Marspacecraft/PaceandLoveKeyboard/Frameware/PaceAndLoveKeyboard/Core/Oled/oled.c

/*
this library is a 0.91'OLED(ssd1306) driver
*/
#include "string.h"
#include "keyconfig.h"
//Header file reference
//The oledfont.h, oled.h and STM32's i2c.h files need to be referenced in the oled.c file
#include "oled.h"
//#include "oledfont.h"
#include "i2c.h"
#include "timertask.h"

#ifdef I2C_OLED

/*************************8*16ASCII*************************/
static uint8_t F8X16[]=
{
	0x02,0x02,0x02,0x02,0x02,0x02,0x02,0x02,0x80,0x80,0x80,0x80,0x80,0x80,0x80,0x80,// 0
	0x02,0x02,0x02,0xFA,0x02,0x02,0x02,0x02,0x80,0x80,0x80,0xB3,0xB0,0x80,0x80,0x80,//! 1
	0x02,0x22,0x1A,0x0E,0x22,0x1A,0x0E,0x02,0x80,0x80,0x80,0x80,0x80,0x80,0x80,0x80,//" 2
	0x42,0xC2,0x7A,0x42,0xC2,0x7A,0x42,0x02,0x84,0xBF,0x84,0x84,0xBF,0x84,0x84,0x80,//# 3
	0x02,0x72,0x8A,0xFE,0x0A,0x32,0x02,0x02,0x80,0x8C,0x90,0xBF,0x91,0x8E,0x80,0x80,//$ 4
	0xF2,0x0A,0xF2,0x02,0xE2,0x1A,0x02,0x02,0x80,0xA1,0x9C,0x83,0x9E,0xA1,0x9E,0x80,//% 5
	0x02,0xF2,0x0A,0x8A,0x72,0x02,0x02,0x02,0x9E,0xA1,0xA3,0xA4,0x99,0xA7,0xA1,0x90,//& 6
	0x22,0x2E,0x1E,0x02,0x02,0x02,0x02,0x02,0x80,0x80,0x80,0x80,0x80,0x80,0x80,0x80,//' 7
	0x02,0x02,0x02,0xE2,0x1A,0x06,0x02,0x02,0x80,0x80,0x80,0x87,0x98,0xA0,0x80,0x80,//( 8
	0x02,0x02,0x06,0x1A,0xE2,0x02,0x02,0x02,0x80,0x80,0xA0,0x98,0x87,0x80,0x00,0x00,//) 9
	0x22,0x42,0x82,0xF2,0x82,0x42,0x22,0x02,0x84,0x82,0x81,0x8F,0x81,0x82,0x84,0x80,//* 10
	0x02,0x02,0x02,0xF2,0x02,0x02,0x02,0x02,0x81,0x81,0x81,0x9F,0x81,0x81,0x81,0x80,//+ 11
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
	0x02,0x02,0x32,0x72,0x72,0x72,0xF2,0xFE,
	0xCF,0x8E,0x9E,0x9E,0x8C,0x80,0xC0,0xFF,//5
	0x06,0x02,0x72,0x72,0x72,0x62,0xE6,0xFE,
	0xC0,0x80,0x9E,0x9E,0x9E,0x80,0xC0,0xFF,//6
	0xF2,0xF2,0x72,0x12,0x02,0x82,0xE2,0xFE,
	0xFF,0xFF,0x80,0x80,0xFF,0xFF,0xFF,0xFF,//7



};
/**
 * 0.91 "OLED initialization control word
 * Each control word can change the display properties of the screen according to the manufacturer's Datasheet
 * For example, in the fifth line from the bottom, the control word 0x81,0x80.you can changes the contrast by changing 0x80
 * 
*/
#if 0
uint8_t initcmd1[] = 
{
	0xAE,		//display off
	0xD5, 0x80, //Set Display Clock Divide Ratio/Oscillator Frequency
	0xA8, 0x1F, //set multiplex Ratio
	0xD3, 0x00, //display offset
	0x40,		//set display start line
	0x8d, 0x14, //set charge pump
	0xa0,		//set segment remap
	0xc0,		//set com output scan direction
	0xda, 0x00, //set com pins hardware configuration
	0x81, 0x80, //set contrast control
	0xd9, 0x1f, //set pre-charge period
	0xdb, 0x40, //set vcom deselect level
	0xa4,		//Set Entire Display On/Off
	0xaf,		//set display on
};
	#endif
	uint8_t initcmd1[] = {
	0xAE,		//display off
	0xD5, 0x80, //Set Display Clock Divide Ratio/Oscillator Frequency
	0xA8, 0x1F, //set multiplex Ratio
	0xD3, 0x00, //display offset
	0x40,		//set display start line
	0x8d, 0x14, //set charge pump
	//0x27,
	//0x2e,
	0xa0,		//set segment remap
	0xc0,		//set com output scan direction
	0xda, 0x00, //set com pins hardware configuration
	0x81, 0x80, //set contrast control
	0xd9, 0x1f, //set pre-charge period
	0xdb, 0x40, //set vcom deselect level
	0xa4,		//Set Entire Display On/Off
	0xaf,		//set display on
};
/**
 * OLED writes commands and data functions
 * OLED writes commands, data functions, and changes the contents of these two functions if you want to migrate them to another development board
 * For example: I use the i2c2 interface, then you only need to change &hi2c1 to &hi2c2.
**/
void OLED_Write_cmd(uint8_t cmd)
{
	HAL_I2C_Mem_Write(&hi2c2, 0x78, 0x00, I2C_MEMADD_SIZE_8BIT, &cmd, 1, 0x100);
}
void OLED_Write_data(uint8_t data)
{
	HAL_I2C_Mem_Write(&hi2c2, 0x78, 0x40, I2C_MEMADD_SIZE_8BIT, &data, 1, 0x100);
}

void OLED_Write_databuffer(uint8_t* data,uint16_t len)
{
	HAL_I2C_Mem_Write(&hi2c2, 0x78, 0x40, I2C_MEMADD_SIZE_8BIT, data, len, 0x100);
}


/**
 * @brief	Image display function
 * @param x0  Image display start position x-axis
 * @param y0  Image display start position y-axis
 * @param x1  Image display end position x-axis 1 - 127
 * @param y1  Image display end position x-axis 1 - 4
 * @param BMP Image display pointer address
 * @note	The image needs to be converted to an array and passed into this function
*/
void OLED_ShowPic(uint8_t x0, uint8_t y0, uint8_t x1, uint8_t y1, uint8_t BMP[])
{
	uint16_t i = 0;
	uint8_t y;
	for (y = y0; y < y1; y++)
	{
		OLED_Set_Position(x0, y);
		OLED_Write_databuffer(&BMP[i],x1-x0);
		i+=x1-x0;
	}
}



/**
 * @brief	Display a float 
 * @param x  position x-axis  0 - 127
 * @param y  position y-axis  0
 * @param num  The order of the Chinese characters in the Hzb[] array
 * @param accuracy Preserve decimal places
 * @param fontsize 8/16
 * @note	
*/
void OLED_ShowFloat(uint8_t x, uint8_t y, float num, uint8_t accuracy)
{
	uint8_t i = 0;
	uint8_t j = 0;
	uint8_t t = 0;
	uint8_t temp = 0;
	uint16_t numel = 0;
	uint32_t integer = 0;
	float decimals = 0;

	//Is a negative number?
	if (num < 0)
	{
		OLED_ShowChar(x, y, '-');
		num = 0 - num;
		i++;
	}

	integer = (uint32_t)num;
	decimals = num - integer;

	//Integer part
	if (integer)
	{
		numel = integer;

		while (numel)
		{
			numel /= 10;
			j++;
		}
		i += (j - 1);
		for (temp = 0; temp < j; temp++)
		{
			OLED_ShowChar(x + 14 * (i - temp), y, integer % 10 + '0'); // 鏄剧ず鏁存暟閮ㄥ垎
			integer /= 10;
		}
	}
	else
	{
		OLED_ShowChar(x + 14 * i, y, temp + '0');
	}
	i++;
	//Decimal part
	if (accuracy)
	{
		OLED_ShowChar(x + 14 * i, y, '.');

		i++;
		for (t = 0; t < accuracy; t++)
		{
			decimals *= 10;
			temp = (uint8_t)decimals;
			OLED_ShowChar(x + 14 * (i + t), y, temp + '0');
			decimals -= temp;
		}
	}
}

/**
 * @brief	OLED pow function
 * @param m - base
 * @param n - exponent
 * @return result
*/
static uint32_t OLED_Pow(uint8_t a, uint8_t n)
{
	uint32_t result = 1;
	while (n--)
	{
		result *= a;
	}
	return result;
}

/**
 * @brief	Display a uint32 Interger
 * @param x  position x-axis  0 - 127
 * @param y  position y-axis  0 - 3
 * @param num  Displayed integers
 * @param length Number of integer digits
 * @note	
*/
void OLED_ShowNum(uint8_t x, uint8_t y, uint32_t num, uint8_t length)
{

	uint8_t t, temp;
	uint8_t enshow = 0;
	for (t = 0; t < length; t++)
	{
		temp = (num / OLED_Pow(10, length - t - 1)) % 10;
		if (enshow == 0 && t < (length - 1))
		{
			if (temp == 0)
			{
				OLED_ShowChar(x + 14 * t, y, ' ');
				continue;
			}
			else
				enshow = 1;
		}
		OLED_ShowChar(x + 14 * t, y, temp + '0');
	}
}


/**
 * @brief	Display ascii string
 * @param x  String start position on the X-axis  range锛? - 127
 * @param y  String start position on the Y-axis  range锛? - 3 
 * @param ch  String pointer
 * @param fontsize You can choose from two fonts 8/16
**/
void OLED_ShowStr(uint8_t x, uint8_t y, char *ch)
{
	uint8_t j = 0;
	while (ch[j] != '\0')
	{
		OLED_ShowChar(x, y, ch[j]);
		x += 8;
		j++;
	}
}

/**
 * @brief	Displays ASCII characters
 * @param x  Character position on the X-axis  range锛? - 127
 * @param y  Character position on the Y-axis  range锛? - 3 
 * @param no  character
 * @param fontsize You can choose from three fonts 8/16
**/
void OLED_ShowChar(uint8_t x, uint8_t y, uint8_t ch)
{
	uint8_t c = 0;
	c = ch - ' ';

	if (x > 127 || y>4) //beyond the right boundary
	{
		return;
	}

	OLED_Set_Position(x, y);
	OLED_Write_databuffer(&F8X16[c * 16],8);

	if(y<3)
	{
		OLED_Set_Position(x, y+1);
		OLED_Write_databuffer(&F8X16[c * 16+8],8);
	}
}


/**
 * OLED fill function, after using the function 0.91 inch oled screen into full white
**/
void OLED_Allfill(void)
{
	uint8_t i, j;
	for (i = 0; i < 4; i++)
	{
		OLED_Write_cmd(0xb0 + i);
		OLED_Write_cmd(0x00);
		OLED_Write_cmd(0x10);
		for (j = 0; j < 128; j++)
		{
			OLED_Write_data(0xFF);
		}
	}
}

/**
 * @brief Set coordinates
 * @param x: X position, range 0 - 127  Because our OLED screen resolution is 128*32, so the horizontal is 128 pixels
 * @param y: Y position, range 0 - 3    Because the vertical pixels are positioned in pages, each page has 8 pixels, so there are 4 pages
**/
void OLED_Set_Position(uint8_t x, uint8_t y)
{
	OLED_Write_cmd(0xb0 + y);
	OLED_Write_cmd(((x & 0xf0) >> 4) | 0x10);
	OLED_Write_cmd((x & 0x0f) | 0x00);
}
/**
 * Clear Screen Function
 * Fill each row and column with 0
**/
void OLED_Clear(void)
{
	uint8_t i, n;
	for (i = 0; i < 4; i++)
	{
		OLED_Write_cmd(0xb0 + i);
		OLED_Write_cmd(0x00);
		OLED_Write_cmd(0x10);
		for (n = 0; n < 128; n++)
		{
			OLED_Write_data(0);
		}
	}
}
/**
 * Turn screen display on and off
**/
void OLED_Display_On(void)
{
	OLED_Write_cmd(0x8D);
	OLED_Write_cmd(0x14);
	OLED_Write_cmd(0xAF);
}
void OLED_Display_Off(void)
{
	OLED_Write_cmd(0x8D);
	OLED_Write_cmd(0x10);
	OLED_Write_cmd(0xAF);
}

/**
 * Initialize the screen
 * Function:send control words one by one
**/
void OLED_Init(void)
{

	HAL_Delay(100);
	uint8_t i;
	for (i = 0; i < sizeof(initcmd1); i++)
	{

		OLED_Write_cmd(initcmd1[i]); //display off
	}

	OLED_Clear();
	OLED_Set_Position(0, 0);
}

///*************************************///


typedef struct
{
	uint8_t 	title_enable;
	uint8_t 	title_flowfg;//列字符溢出标志	
	
	uint16_t 	title_buflen;
	uint16_t 	title_showpos;//列显示开始位置
	uint8_t 	title_showposdelay;//列滚动开始延时
	
	
}oledtile;


typedef struct
{
	oledtile titles[OLED_BUFFER_HEIGHT];
	
	uint8_t line_showorder[OLED_BUFFER_HEIGHT];//滚动显示列顺序队列
	uint8_t linepos;//当前起始显示队列
	uint8_t linenum;//显示列个数
	
}oledbufmsg_t;

static oledbufmsg_t sg_oledbuffermsg = {0};
static uint8_t sg_oledbuffer[2*OLED_BUFFER_HEIGHT][OLED_BUFFER_WIDTH] ={0};


static void Oled_Title2ShowOrder(uint8_t title)
{
	uint8_t i=0;
	for(i=0;i<sg_oledbuffermsg.linenum;i++)
	{
		if(sg_oledbuffermsg.line_showorder[i] == title)
			return;

	}

	if(i<OLED_BUFFER_HEIGHT)
	{
		sg_oledbuffermsg.line_showorder[i] = title;
		sg_oledbuffermsg.linenum++;
	}
}

void OLED_CharMode_SetShowOrder(uint8_t* titles)
{
	uint8_t i;
	for(i=0;i<OLED_BUFFER_HEIGHT;i++)
	{
		if(OLED_TITLE_NULL <= titles[i])
		{	
			break;
		}
		sg_oledbuffermsg.line_showorder[i] = titles[i];
	}

	sg_oledbuffermsg.linenum = i;
	sg_oledbuffermsg.linepos = 0;
}

void OLED_CharMode_ClearShowOrder()
{
	sg_oledbuffermsg.linenum = 0;
	sg_oledbuffermsg.linepos = 0;

}


static void Oled_ShowTitle2Line(uint8_t title,uint8_t line)
{
	uint16_t i = 0;
	uint16_t title_buflen;
	uint16_t title_showpos;//列显示开始位置
	uint8_t j;

	if(title>=OLED_BUFFER_HEIGHT || line>=2)
		return;

	line = line << 1;
	if(0 == sg_oledbuffermsg.titles[title].title_enable)
		return;

	title_buflen = sg_oledbuffermsg.titles[title].title_buflen;
	title_showpos = sg_oledbuffermsg.titles[title].title_showpos;
	title = title << 1;
	for(j=0;j<2;j++,line++)
	{
		OLED_Set_Position(0, line);
		
		OLED_Write_databuffer(&sg_oledbuffer[title+j][0], 8);
		
		i = title_buflen - title_showpos;
		if(i>120)
		{
			i = 120;
		}
		OLED_Write_databuffer(&sg_oledbuffer[title+j][title_showpos], i);
		
		i+=8;
		for (; i <OLED_WIDTH; i++)
		{
			OLED_Write_data(0x00);
		}
	}
}


static uint8_t Oled_Append2Title(uint8_t title,uint8_t* font,uint16_t len)
{
	oledtile* titlemsg;
	uint8_t ret = true;
	if(title>=OLED_BUFFER_HEIGHT)
		return false;

	titlemsg = &sg_oledbuffermsg.titles[title];

	if((len + titlemsg->title_buflen)>OLED_BUFFER_WIDTH)
	{
		len = OLED_BUFFER_WIDTH - titlemsg->title_buflen;
		ret = false;
	}

	if(titlemsg->title_buflen>OLED_WIDTH)
	{
		titlemsg->title_flowfg = 1;
	}

	title = title << 1;
	memcpy(sg_oledbuffer[title]+titlemsg->title_buflen,font,len);
	memcpy(sg_oledbuffer[title+1]+titlemsg->title_buflen,font+len,len);
	titlemsg->title_buflen += len;
	return ret;
	
}

static void Oled_Reset2Title(uint8_t title,uint8_t* font,uint16_t len)
{
	oledtile* titlemsg;
	if(title>=OLED_BUFFER_HEIGHT)
		return;
	
	titlemsg = &sg_oledbuffermsg.titles[title];
	if(NULL == font)
	{
		titlemsg->title_enable = 0;
		return;
	}
	titlemsg->title_enable = 1;
	titlemsg->title_buflen = 8;
	titlemsg->title_showpos = 8;
	titlemsg->title_showposdelay = 15;
	

	
	memcpy(sg_oledbuffer[2*title],&TITLEF[16*title],8);
	memcpy(sg_oledbuffer[2*title+1],&TITLEF[16*title+8],8);

	Oled_Append2Title(title,font,len);

}

static void Oled_Flush_Line(uint8_t lineflushfg)
{
	uint8_t line,title,i,num;
	oledtile* titlemsg;
	num = (2<sg_oledbuffermsg.linenum)?2:sg_oledbuffermsg.linenum;

	line=sg_oledbuffermsg.linepos;
	
	for(i=0;i<num;)
	{	
		title = sg_oledbuffermsg.line_showorder[line];
		titlemsg = &sg_oledbuffermsg.titles[title];
		if(titlemsg->title_enable)
		{
			if(lineflushfg)//刷新所有行
			{
				Oled_ShowTitle2Line(title,i);
			}
			else
			{//只刷新溢出行
				if(titlemsg->title_flowfg)
				{
					if(0==titlemsg->title_showposdelay)
					{
						titlemsg->title_showpos += 2;
						if((titlemsg->title_buflen - titlemsg->title_showpos)<=80)
						{
							titlemsg->title_showpos = 8;
							titlemsg->title_showposdelay = 15;
						}
						Oled_ShowTitle2Line(title,i);
					}
					else
					{
						titlemsg->title_showposdelay--;
					}
				}
			}
			i++;
		}
		
		line++;
		line %= sg_oledbuffermsg.linenum;
		if(line == sg_oledbuffermsg.linepos)
		{
			break;
		}
	}
}

void OLED_CharMode_ShowString(uint8_t title,uint8_t* string)
{
	uint16_t i,len;
	if(title>=OLED_BUFFER_HEIGHT || string[0] < ' ')
		return;

	Oled_Reset2Title(title,&F8X16[(string[0]-' ')*16],8);
	len = strlen((char*)string);
	for(i=1;i<len;i++)
	{
		if(false == Oled_Append2Title(title,&F8X16[(string[i]-' ')*16],8))
		{
			break;
		}
	}
	Oled_Title2ShowOrder(title);
	Oled_Flush_Line(true);
}

void OLED_CharMode_ShowStringAppend(uint8_t title,uint8_t* string)
{
	uint16_t i,len;
	if(title>=OLED_BUFFER_HEIGHT)
		return;
	len = strlen((char*)string);
	for(i=0;i<len;i++)
	{
		if(false == Oled_Append2Title(title,&F8X16[(string[i]-' ')*16],8))
		{
			break;
		}
	}
	
	Oled_Flush_Line(true);
}



void OLED_CharMode_Flush(uint8_t* arg)
{
	static uint8_t linetime = 30;

	if((sg_oledbuffermsg.linenum > 2)&&(0 == linetime))
	{
		sg_oledbuffermsg.linepos += 2;
		if(sg_oledbuffermsg.linepos >= sg_oledbuffermsg.linenum)
			sg_oledbuffermsg.linepos = 0;
		linetime = 30;
		Oled_Flush_Line(true);
		return;
	}
	linetime--;

	Oled_Flush_Line(false);

}




static CycleTimerHandler* sg_oledtimer = NULL;

void OLED_CharMode_DeInit()
{
	if(sg_oledtimer)
	{
		Stop_CycleTimer(sg_oledtimer);
		sg_oledtimer = NULL;
	}
	OLED_Display_Off();
}

void OLED_CharMode_Init()
{
	memset(sg_oledbuffer,0,sizeof(sg_oledbuffer));
	memset(&sg_oledbuffermsg,0,sizeof(sg_oledbuffermsg));
	OLED_Clear();
	OLED_Set_Position(0, 0);
	
	if(NULL == sg_oledtimer)
	{
		sg_oledtimer = Start_CycleTimer(TIMER_PERIOD_100MS,OLED_CharMode_Flush,NULL);
	}
	OLED_Display_On();
}

uint8_t ikun[512] = { /* 0XE3,0X01,0X20,0X00,0X80,0X00, */
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

};




void ginisobeautiful()
{
	
	OLED_Init();
	/*
	uint8_t i,j;

	for(j=0;j<90;j++)
	{
		for(i=0;i<SHARINGAN_NUM;i++)
		{
			OLED_ShowPic(0,0,32,4,Sharingan[i]);
			HAL_Delay(10);
		}
	}
	*/
	OLED_ShowPic(0,0,128,4,ikun);

	
}


#ifdef TEST_OLED
#include "tracelog.h"

unsigned char BMP1[] =
{
 
0x00,0x00,0x00,0x00,0x00,0xE0,0xF8,0x7C,0x0E,0x06,0x87,0x87,0x87,0x87,0x87,0x87,
0x87,0x87,0x87,0x87,0x87,0x87,0x87,0x87,0x87,0x87,0x87,0x0E,0x1E,0xFC,0xF8,0xE0,
0x80,0xE0,0xF0,0x38,0x38,0xFF,0xFF,0x00,0x00,0x00,0xC1,0xE1,0xC1,0x01,0x01,0x01,
0xC1,0xC1,0xC1,0xC1,0xC1,0xC1,0xC1,0xC1,0xC1,0xC1,0xC1,0x00,0x00,0xFF,0xFF,0xFF,
0xFF,0xFF,0xFF,0x00,0x00,0xFF,0xFF,0x00,0x00,0x00,0x18,0x18,0x18,0x18,0x18,0x18,
0x18,0x00,0x00,0x00,0x18,0x18,0x18,0x18,0x18,0x18,0x18,0x00,0x00,0xFF,0xFF,0xFF,
0x07,0x1F,0x3F,0x78,0x70,0xE3,0xE3,0xE0,0xC0,0xC0,0xC3,0xC3,0xC3,0xC3,0xC3,0xC3,
0xC3,0xC0,0xC0,0xC0,0xC3,0xC3,0xC3,0xC3,0xE0,0xE0,0xE0,0x70,0x78,0x3F,0x1F,0x07,/*"C:\Users\kkk\Desktop\news.bmp",0*/ 
};


void test_oled()
{
	float numberfu=-12.1;

	OLED_Allfill();
    HAL_Delay(500);

	OLED_Clear();
    //OLED_ShowPic(90,0,122,4,BMP1);
	//HAL_Delay(5000);
	//OLED_ShowStr(0,3,"Hello");
	//OLED_ShowFloat(50,0,numberfu,3);
	OLED_ShowStr(0,0,"Hello World");
	//OLED_ShowStr(0,1,"I.m");
	OLED_ShowStr(0,2,"I'm Marspacecraft!");
	HAL_Delay(5000);
	//OLED_Clear();
}

void test_charmode()
{
	OLED_CharMode_Init();
	OLED_CharMode_ShowString(OLED_TITLE_0,"Hello0 abcdefghijklmnopqrstuw");
	OLED_CharMode_ShowString(OLED_TITLE_1,"Hello1");
	OLED_CharMode_ShowString(OLED_TITLE_3,"Hello3");
	OLED_CharMode_ShowString(OLED_TITLE_4,"Hello4");
	OLED_CharMode_ShowString(OLED_TITLE_7,"Hello7");
	OLED_CharMode_ShowString(OLED_TITLE_6,"Hello6");
	HAL_Delay(3000);
}

void test_charmodeflush()
{
	OLED_CharMode_Init();
	
	OLED_CharMode_ShowString(OLED_TITLE_0,"Hello0");
	OLED_CharMode_ShowString(OLED_TITLE_1,"Hello1 abcdefghijklmnopqrstuw");
	OLED_CharMode_ShowString(OLED_TITLE_2,"Hello2");
	OLED_CharMode_ShowString(OLED_TITLE_3,"Hello3 abcdefghijklmnopqrstuw");
	OLED_CharMode_ShowString(OLED_TITLE_4,"Hello4 abcdefghijklmnopqrstuw");
	OLED_CharMode_ShowString(OLED_TITLE_5,"Hello5 abcdefghijklmnopqrstuw");
	
	while(1)
	{
		OLED_CharMode_Flush(NULL);
		HAL_Delay(100);
	}
}
void testcase_oled()
{
	TRACELOG_DEBUG("Running testcase_oled");
	//test_oled();
	test_charmode();
	//test_charmodeflush();
	TRACELOG_DEBUG("Testcase_oled end");
}

#endif

#endif
