Marspacecraft/PaceandLoveKeyboard/Frameware/PaceAndLoveKeyboard/Core/Src/spi.c

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
/* Includes ------------------------------------------------------------------*/
#include "spi.h"

/* USER CODE BEGIN 0 */
volatile static EXT_CSFUNC sg_EXT_SPI_CsFunc = NULL;

/* USER CODE END 0 */

SPI_HandleTypeDef hspi1;
SPI_HandleTypeDef hspi2;
SPI_HandleTypeDef hspi3;
DMA_HandleTypeDef hdma_spi2_tx;
DMA_HandleTypeDef hdma_spi3_rx;
DMA_HandleTypeDef hdma_spi3_tx;

/* SPI1 init function */
void MX_SPI1_Init(void)
{

  /* USER CODE BEGIN SPI1_Init 0 */
  GPIO_InitTypeDef GPIO_InitStruct = {0};

  /* USER CODE END SPI1_Init 0 */

  hspi1.Instance = SPI1;
  hspi1.Init.Mode = SPI_MODE_MASTER;
  hspi1.Init.Direction = SPI_DIRECTION_2LINES_RXONLY;
  hspi1.Init.DataSize = SPI_DATASIZE_8BIT;
  hspi1.Init.CLKPolarity = SPI_POLARITY_HIGH;
  hspi1.Init.CLKPhase = SPI_PHASE_1EDGE;
  hspi1.Init.NSS = SPI_NSS_SOFT;
  hspi1.Init.BaudRatePrescaler = SPI_BAUDRATEPRESCALER_16;
  hspi1.Init.FirstBit = SPI_FIRSTBIT_MSB;
  hspi1.Init.TIMode = SPI_TIMODE_DISABLE;
  hspi1.Init.CRCCalculation = SPI_CRCCALCULATION_DISABLE;
  hspi1.Init.CRCPolynomial = 10;
  if (HAL_SPI_Init(&hspi1) != HAL_OK)
  {
    Error_Handler();
  }
  /* USER CODE BEGIN SPI1_Init 2 */
	__HAL_RCC_GPIOA_CLK_ENABLE(); 	  
	GPIO_InitStruct.Pin =  KEY_PL_Pin;  
	GPIO_InitStruct.Mode	= GPIO_MODE_OUTPUT_PP;	
	GPIO_InitStruct.Pull	= GPIO_PULLUP;
	GPIO_InitStruct.Speed = GPIO_SPEED_FREQ_HIGH;
	HAL_GPIO_Init(KEY_PL_GPIO_Port, &GPIO_InitStruct);  
	  
	  
	HAL_GPIO_WritePin(KEY_PL_GPIO_Port,KEY_PL_Pin,GPIO_PIN_RESET);

  /* USER CODE END SPI1_Init 2 */

}
/* SPI2 init function */
void MX_SPI2_Init(void)
{

  hspi2.Instance = SPI2;
  hspi2.Init.Mode = SPI_MODE_MASTER;
  hspi2.Init.Direction = SPI_DIRECTION_2LINES;
  hspi2.Init.DataSize = SPI_DATASIZE_8BIT;
  hspi2.Init.CLKPolarity = SPI_POLARITY_LOW;
  hspi2.Init.CLKPhase = SPI_PHASE_1EDGE;
  hspi2.Init.NSS = SPI_NSS_SOFT;
  hspi2.Init.BaudRatePrescaler = SPI_BAUDRATEPRESCALER_64;
  hspi2.Init.FirstBit = SPI_FIRSTBIT_MSB;
  hspi2.Init.TIMode = SPI_TIMODE_DISABLE;
  hspi2.Init.CRCCalculation = SPI_CRCCALCULATION_DISABLE;
  hspi2.Init.CRCPolynomial = 10;
  if (HAL_SPI_Init(&hspi2) != HAL_OK)
  {
    Error_Handler();
  }
}
/* SPI3 init function */
void MX_SPI3_Init(void)
{

  hspi3.Instance = SPI3;
  hspi3.Init.Mode = SPI_MODE_MASTER;
  hspi3.Init.Direction = SPI_DIRECTION_2LINES;
  hspi3.Init.DataSize = SPI_DATASIZE_8BIT;
  hspi3.Init.CLKPolarity = SPI_POLARITY_LOW;
  hspi3.Init.CLKPhase = SPI_PHASE_1EDGE;
  hspi3.Init.NSS = SPI_NSS_SOFT;
  hspi3.Init.BaudRatePrescaler = SPI_BAUDRATEPRESCALER_16;
  hspi3.Init.FirstBit = SPI_FIRSTBIT_MSB;
  hspi3.Init.TIMode = SPI_TIMODE_DISABLE;
  hspi3.Init.CRCCalculation = SPI_CRCCALCULATION_DISABLE;
  hspi3.Init.CRCPolynomial = 10;
  if (HAL_SPI_Init(&hspi3) != HAL_OK)
  {
    Error_Handler();
  }
}

void HAL_SPI_MspInit(SPI_HandleTypeDef* spiHandle)
{

  GPIO_InitTypeDef GPIO_InitStruct = {0};
  if(spiHandle->Instance==SPI1)
  {
    /* SPI1 clock enable */
    __HAL_RCC_SPI1_CLK_ENABLE();

    __HAL_RCC_GPIOA_CLK_ENABLE();
    /**SPI1 GPIO Configuration
    PA5     ------> SPI1_SCK
    PA6     ------> SPI1_MISO
    */
    GPIO_InitStruct.Pin = KEY_SPI1_SCK_Pin;
    GPIO_InitStruct.Mode = GPIO_MODE_AF_PP;
    GPIO_InitStruct.Speed = GPIO_SPEED_FREQ_HIGH;
    HAL_GPIO_Init(KEY_SPI1_SCK_GPIO_Port, &GPIO_InitStruct);

    GPIO_InitStruct.Pin = KEY_SPI1_MISO_Pin;
    GPIO_InitStruct.Mode = GPIO_MODE_INPUT;
    GPIO_InitStruct.Pull = GPIO_NOPULL;
    HAL_GPIO_Init(KEY_SPI1_MISO_GPIO_Port, &GPIO_InitStruct);

  }
  else if(spiHandle->Instance==SPI2)
  {
    /* SPI2 clock enable */
    __HAL_RCC_SPI2_CLK_ENABLE();

    __HAL_RCC_GPIOB_CLK_ENABLE();
    /**SPI2 GPIO Configuration
    PB13     ------> SPI2_SCK
    PB14     ------> SPI2_MISO
    PB15     ------> SPI2_MOSI
    */
    GPIO_InitStruct.Pin = EXT_SPI2_CLK_Pin|EXT_SPI2_MOSI_Pin;
    GPIO_InitStruct.Mode = GPIO_MODE_AF_PP;
    GPIO_InitStruct.Speed = GPIO_SPEED_FREQ_HIGH;
    HAL_GPIO_Init(GPIOB, &GPIO_InitStruct);

    GPIO_InitStruct.Pin = EXT_SPI2_MISO_Pin;
    GPIO_InitStruct.Mode = GPIO_MODE_INPUT;
    GPIO_InitStruct.Pull = GPIO_NOPULL;
    HAL_GPIO_Init(EXT_SPI2_MISO_GPIO_Port, &GPIO_InitStruct);

    /* SPI2 DMA Init */
    /* SPI2_TX Init */
    hdma_spi2_tx.Instance = DMA1_Channel5;
    hdma_spi2_tx.Init.Direction = DMA_MEMORY_TO_PERIPH;
    hdma_spi2_tx.Init.PeriphInc = DMA_PINC_DISABLE;
    hdma_spi2_tx.Init.MemInc = DMA_MINC_ENABLE;
    hdma_spi2_tx.Init.PeriphDataAlignment = DMA_PDATAALIGN_BYTE;
    hdma_spi2_tx.Init.MemDataAlignment = DMA_MDATAALIGN_BYTE;
    hdma_spi2_tx.Init.Mode = DMA_NORMAL;
    hdma_spi2_tx.Init.Priority = DMA_PRIORITY_LOW;
    if (HAL_DMA_Init(&hdma_spi2_tx) != HAL_OK)
    {
      Error_Handler();
    }

    __HAL_LINKDMA(spiHandle,hdmatx,hdma_spi2_tx);

  }
  else if(spiHandle->Instance==SPI3)
  {
    /* SPI3 clock enable */
    __HAL_RCC_SPI3_CLK_ENABLE();

    __HAL_RCC_GPIOB_CLK_ENABLE();
    /**SPI3 GPIO Configuration
    PB3     ------> SPI3_SCK
    PB4     ------> SPI3_MISO
    PB5     ------> SPI3_MOSI
    */
    GPIO_InitStruct.Pin = FLASH_SPI3_CLK_Pin|FLASH_SPI3_MOSI_Pin;
    GPIO_InitStruct.Mode = GPIO_MODE_AF_PP;
    GPIO_InitStruct.Speed = GPIO_SPEED_FREQ_HIGH;
    HAL_GPIO_Init(GPIOB, &GPIO_InitStruct);

    GPIO_InitStruct.Pin = FLASH_SPI3_MISO_Pin;
    GPIO_InitStruct.Mode = GPIO_MODE_INPUT;
    GPIO_InitStruct.Pull = GPIO_NOPULL;
    HAL_GPIO_Init(FLASH_SPI3_MISO_GPIO_Port, &GPIO_InitStruct);

    /* SPI3 DMA Init */
    /* SPI3_RX Init */
    hdma_spi3_rx.Instance = DMA2_Channel1;
    hdma_spi3_rx.Init.Direction = DMA_PERIPH_TO_MEMORY;
    hdma_spi3_rx.Init.PeriphInc = DMA_PINC_DISABLE;
    hdma_spi3_rx.Init.MemInc = DMA_MINC_ENABLE;
    hdma_spi3_rx.Init.PeriphDataAlignment = DMA_PDATAALIGN_BYTE;
    hdma_spi3_rx.Init.MemDataAlignment = DMA_MDATAALIGN_BYTE;
    hdma_spi3_rx.Init.Mode = DMA_NORMAL;
    hdma_spi3_rx.Init.Priority = DMA_PRIORITY_LOW;
    if (HAL_DMA_Init(&hdma_spi3_rx) != HAL_OK)
    {
      Error_Handler();
    }

    __HAL_LINKDMA(spiHandle,hdmarx,hdma_spi3_rx);

    /* SPI3_TX Init */
    hdma_spi3_tx.Instance = DMA2_Channel2;
    hdma_spi3_tx.Init.Direction = DMA_MEMORY_TO_PERIPH;
    hdma_spi3_tx.Init.PeriphInc = DMA_PINC_DISABLE;
    hdma_spi3_tx.Init.MemInc = DMA_MINC_ENABLE;
    hdma_spi3_tx.Init.PeriphDataAlignment = DMA_PDATAALIGN_BYTE;
    hdma_spi3_tx.Init.MemDataAlignment = DMA_MDATAALIGN_BYTE;
    hdma_spi3_tx.Init.Mode = DMA_NORMAL;
    hdma_spi3_tx.Init.Priority = DMA_PRIORITY_LOW;
    if (HAL_DMA_Init(&hdma_spi3_tx) != HAL_OK)
    {
      Error_Handler();
    }

    __HAL_LINKDMA(spiHandle,hdmatx,hdma_spi3_tx);

  }
}

void HAL_SPI_MspDeInit(SPI_HandleTypeDef* spiHandle)
{

  if(spiHandle->Instance==SPI1)
  {
    /* Peripheral clock disable */
    __HAL_RCC_SPI1_CLK_DISABLE();

    /**SPI1 GPIO Configuration
    PA5     ------> SPI1_SCK
    PA6     ------> SPI1_MISO
    */
    HAL_GPIO_DeInit(GPIOA, KEY_SPI1_SCK_Pin|KEY_SPI1_MISO_Pin);

  }
  else if(spiHandle->Instance==SPI2)
  {
    /* Peripheral clock disable */
    __HAL_RCC_SPI2_CLK_DISABLE();

    /**SPI2 GPIO Configuration
    PB13     ------> SPI2_SCK
    PB14     ------> SPI2_MISO
    PB15     ------> SPI2_MOSI
    */
    HAL_GPIO_DeInit(GPIOB, EXT_SPI2_CLK_Pin|EXT_SPI2_MISO_Pin|EXT_SPI2_MOSI_Pin);

    /* SPI2 DMA DeInit */
    HAL_DMA_DeInit(spiHandle->hdmatx);
  }
  else if(spiHandle->Instance==SPI3)
  {
    /* Peripheral clock disable */
    __HAL_RCC_SPI3_CLK_DISABLE();

    /**SPI3 GPIO Configuration
    PB3     ------> SPI3_SCK
    PB4     ------> SPI3_MISO
    PB5     ------> SPI3_MOSI
    */
    HAL_GPIO_DeInit(GPIOB, FLASH_SPI3_CLK_Pin|FLASH_SPI3_MISO_Pin|FLASH_SPI3_MOSI_Pin);

    /* SPI3 DMA DeInit */
    HAL_DMA_DeInit(spiHandle->hdmarx);
    HAL_DMA_DeInit(spiHandle->hdmatx);
  }
}

/* USER CODE BEGIN 1 */
#include "main.h"
HAL_StatusTypeDef EXT_SPI_read_write(uint8_t *pRxData, uint8_t *pTxData,uint16_t Size,EXT_CSFUNC csfunc)
{
	HAL_StatusTypeDef ret;
	if (EXT_SPI_HANDLER.State != HAL_SPI_STATE_READY)
  	{
    	return HAL_BUSY;
  	}

	if(csfunc != sg_EXT_SPI_CsFunc)
		return HAL_BUSY;
	
	//sg_EXT_SPI3_DmaTxCallBack = NULL;
	//sg_EXT_SPI3_DmaRxCallBack = NULL;
	__DMB();

	//csfunc(true);
	ret = HAL_SPI_TransmitReceive(&EXT_SPI_HANDLER,pTxData,pRxData, Size, 1000);

	//csfunc(false);

	
	
	return ret;
}

HAL_StatusTypeDef EXT_SPI_read(uint8_t *pRxData,uint16_t Size,EXT_CSFUNC csfunc)
{
	HAL_StatusTypeDef ret;
	
	if (EXT_SPI_HANDLER.State != HAL_SPI_STATE_READY)
  	{
    	return HAL_BUSY;
  	}

	if(csfunc != sg_EXT_SPI_CsFunc)
		return HAL_BUSY;
	
	//sg_EXT_SPI3_DmaRxCallBack = NULL;
	__DMB();

	//csfunc(true);
	ret = HAL_SPI_Receive(&EXT_SPI_HANDLER,pRxData, Size, 1000);

	//csfunc(false);

	
	
	return ret;
}

HAL_StatusTypeDef EXT_SPI_write(uint8_t *pTxData,uint16_t Size,EXT_CSFUNC csfunc)
{
	HAL_StatusTypeDef ret;
	
	if (EXT_SPI_HANDLER.State != HAL_SPI_STATE_READY)
  	{
    	return HAL_BUSY;
  	}

	if(csfunc != sg_EXT_SPI_CsFunc)
		return HAL_BUSY;
	
	//sg_EXT_SPI3_DmaTxCallBack = NULL;
	__DMB();

	//csfunc(true);
	ret = HAL_SPI_Transmit(&EXT_SPI_HANDLER,pTxData, Size, 1000);

	//csfunc(false);
	
	
	
	return ret;
}



HAL_StatusTypeDef EXT_SPI_read_write_byte(uint8_t *pRxData, uint8_t TxData,EXT_CSFUNC csfunc)
{
	return EXT_SPI_read_write(pRxData,&TxData,1,csfunc);
}

HAL_StatusTypeDef EXT_SPI_read_byte(uint8_t *pRxData,EXT_CSFUNC csfunc)
{
	return EXT_SPI_read(pRxData,1,csfunc);
}

HAL_StatusTypeDef EXT_SPI_write_byte(uint8_t TxData,EXT_CSFUNC csfunc)
{
	return EXT_SPI_write(&TxData,1,csfunc);
}


bool EXT_SPI_OccupyBus(EXT_CSFUNC csfunc)
{
	bool ret ;
	
	ret = KB_ATOMIC_CAS_ADDR((volatile void **)&sg_EXT_SPI_CsFunc,NULL,csfunc);
	if(ret)
		csfunc(true);
	return ret;
}

void EXT_SPI_FreeBus(EXT_CSFUNC csfunc)
{
	csfunc(false);
	KB_ATOMIC_CAS_ADDR((volatile void **)&sg_EXT_SPI_CsFunc,sg_EXT_SPI_CsFunc,NULL);
}

/* USER CODE END 1 */
