Marspacecraft/PaceandLoveKeyboard/Frameware/PaceAndLoveKeyboard/Core/Src/tim.c

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
/* Includes ------------------------------------------------------------------*/
#include "tim.h"

/* USER CODE BEGIN 0 */
#include "timertask.h"
#include "scheduler.h"
/* USER CODE END 0 */

TIM_HandleTypeDef htim6;
TIM_HandleTypeDef htim8;
DMA_HandleTypeDef hdma_tim8_ch1;

/* TIM6 init function */
void MX_TIM6_Init(void)
{

  TIM_MasterConfigTypeDef sMasterConfig = {0};

  /* USER CODE BEGIN TIM6_Init 1 */
	// 72Mhz 10ms interrupt
  /* USER CODE END TIM6_Init 1 */
  htim6.Instance = TIM6;
  htim6.Init.Prescaler = 36000;
  htim6.Init.CounterMode = TIM_COUNTERMODE_UP;
  htim6.Init.Period = 10;
  htim6.Init.AutoReloadPreload = TIM_AUTORELOAD_PRELOAD_ENABLE;
  if (HAL_TIM_Base_Init(&htim6) != HAL_OK)
  {
    Error_Handler();
  }
  sMasterConfig.MasterOutputTrigger = TIM_TRGO_RESET;
  sMasterConfig.MasterSlaveMode = TIM_MASTERSLAVEMODE_DISABLE;
  if (HAL_TIMEx_MasterConfigSynchronization(&htim6, &sMasterConfig) != HAL_OK)
  {
    Error_Handler();
  }
  /* USER CODE BEGIN TIM6_Init 2 */
  HAL_TIM_Base_Start_IT(&htim6);
  /* USER CODE END TIM6_Init 2 */

}
/* TIM8 init function */
void MX_TIM8_Init(void)
{

  TIM_MasterConfigTypeDef sMasterConfig = {0};
  TIM_OC_InitTypeDef sConfigOC = {0};
  TIM_BreakDeadTimeConfigTypeDef sBreakDeadTimeConfig = {0};

  htim8.Instance = TIM8;
  htim8.Init.Prescaler = 0;
  htim8.Init.CounterMode = TIM_COUNTERMODE_UP;
  htim8.Init.Period = 89;
  htim8.Init.ClockDivision = TIM_CLOCKDIVISION_DIV1;
  htim8.Init.RepetitionCounter = 0;
  htim8.Init.AutoReloadPreload = TIM_AUTORELOAD_PRELOAD_DISABLE;
  if (HAL_TIM_PWM_Init(&htim8) != HAL_OK)
  {
    Error_Handler();
  }
  sMasterConfig.MasterOutputTrigger = TIM_TRGO_RESET;
  sMasterConfig.MasterSlaveMode = TIM_MASTERSLAVEMODE_DISABLE;
  if (HAL_TIMEx_MasterConfigSynchronization(&htim8, &sMasterConfig) != HAL_OK)
  {
    Error_Handler();
  }
  sConfigOC.OCMode = TIM_OCMODE_PWM1;
  sConfigOC.Pulse = 0;
  sConfigOC.OCPolarity = TIM_OCPOLARITY_HIGH;
  sConfigOC.OCNPolarity = TIM_OCNPOLARITY_HIGH;
  sConfigOC.OCFastMode = TIM_OCFAST_DISABLE;
  sConfigOC.OCIdleState = TIM_OCIDLESTATE_RESET;
  sConfigOC.OCNIdleState = TIM_OCNIDLESTATE_RESET;
  if (HAL_TIM_PWM_ConfigChannel(&htim8, &sConfigOC, TIM_CHANNEL_1) != HAL_OK)
  {
    Error_Handler();
  }
  sBreakDeadTimeConfig.OffStateRunMode = TIM_OSSR_DISABLE;
  sBreakDeadTimeConfig.OffStateIDLEMode = TIM_OSSI_DISABLE;
  sBreakDeadTimeConfig.LockLevel = TIM_LOCKLEVEL_OFF;
  sBreakDeadTimeConfig.DeadTime = 0;
  sBreakDeadTimeConfig.BreakState = TIM_BREAK_DISABLE;
  sBreakDeadTimeConfig.BreakPolarity = TIM_BREAKPOLARITY_HIGH;
  sBreakDeadTimeConfig.AutomaticOutput = TIM_AUTOMATICOUTPUT_DISABLE;
  if (HAL_TIMEx_ConfigBreakDeadTime(&htim8, &sBreakDeadTimeConfig) != HAL_OK)
  {
    Error_Handler();
  }
  HAL_TIM_MspPostInit(&htim8);

}

void HAL_TIM_Base_MspInit(TIM_HandleTypeDef* tim_baseHandle)
{

  if(tim_baseHandle->Instance==TIM6)
  {
    /* TIM6 clock enable */
    __HAL_RCC_TIM6_CLK_ENABLE();

    /* TIM6 interrupt Init */
    HAL_NVIC_SetPriority(TIM6_IRQn, 0, 0);
    HAL_NVIC_EnableIRQ(TIM6_IRQn);
  }
}

void HAL_TIM_PWM_MspInit(TIM_HandleTypeDef* tim_pwmHandle)
{

  if(tim_pwmHandle->Instance==TIM8)
  {
    /* TIM8 clock enable */
    __HAL_RCC_TIM8_CLK_ENABLE();

    /* TIM8 DMA Init */
    /* TIM8_CH1 Init */
    hdma_tim8_ch1.Instance = DMA2_Channel3;
    hdma_tim8_ch1.Init.Direction = DMA_MEMORY_TO_PERIPH;
    hdma_tim8_ch1.Init.PeriphInc = DMA_PINC_DISABLE;
    hdma_tim8_ch1.Init.MemInc = DMA_MINC_ENABLE;
    hdma_tim8_ch1.Init.PeriphDataAlignment = DMA_PDATAALIGN_HALFWORD;
    hdma_tim8_ch1.Init.MemDataAlignment = DMA_MDATAALIGN_HALFWORD;
    hdma_tim8_ch1.Init.Mode = DMA_NORMAL;
    hdma_tim8_ch1.Init.Priority = DMA_PRIORITY_MEDIUM;
    if (HAL_DMA_Init(&hdma_tim8_ch1) != HAL_OK)
    {
      Error_Handler();
    }

    __HAL_LINKDMA(tim_pwmHandle,hdma[TIM_DMA_ID_CC1],hdma_tim8_ch1);

  }
}
void HAL_TIM_MspPostInit(TIM_HandleTypeDef* timHandle)
{

  GPIO_InitTypeDef GPIO_InitStruct = {0};
  if(timHandle->Instance==TIM8)
  {
    __HAL_RCC_GPIOC_CLK_ENABLE();
    /**TIM8 GPIO Configuration
    PC6     ------> TIM8_CH1
    */
    GPIO_InitStruct.Pin = RGB_PWM_Pin;
    GPIO_InitStruct.Mode = GPIO_MODE_AF_PP;
    GPIO_InitStruct.Speed = GPIO_SPEED_FREQ_LOW;
    HAL_GPIO_Init(RGB_PWM_GPIO_Port, &GPIO_InitStruct);

  }

}

void HAL_TIM_Base_MspDeInit(TIM_HandleTypeDef* tim_baseHandle)
{

  if(tim_baseHandle->Instance==TIM6)
  {
    /* Peripheral clock disable */
    __HAL_RCC_TIM6_CLK_DISABLE();

    /* TIM6 interrupt Deinit */
    HAL_NVIC_DisableIRQ(TIM6_IRQn);
  }
}

void HAL_TIM_PWM_MspDeInit(TIM_HandleTypeDef* tim_pwmHandle)
{

  if(tim_pwmHandle->Instance==TIM8)
  {
    /* Peripheral clock disable */
    __HAL_RCC_TIM8_CLK_DISABLE();

    /* TIM8 DMA DeInit */
    HAL_DMA_DeInit(tim_pwmHandle->hdma[TIM_DMA_ID_CC1]);
  }
}

/* USER CODE BEGIN 1 */

static uint16_t sg_MS_Count = 0;

void HAL_TIM_PeriodElapsedCallback(TIM_HandleTypeDef *htim)
{
	tSched_Itemer item;
	uint16_t count = 0;
    if (htim->Instance == TIM6)
    {
       	sg_MS_Count++;//5ms
		if(0 == (sg_MS_Count%2))//10ms
		{
			count = sg_MS_Count;
			count = sg_MS_Count/2;
			item.size = count;
			item.handler = CycleTimer_Task;
			item.event = EVENT_CYCLE_TIMER;
			push_2_scheduler(&item);
		}
    }

}
//5ms
uint16_t TIM_GetCounnt_MS()
{
	return sg_MS_Count;
}






/* USER CODE END 1 */
