Marspacecraft/PaceandLoveKeyboard/Frameware/PaceAndLoveKeyboard/Core/Fronts/gt20.h

#ifndef _GT_20_H_
#define _GT_20_H_

#include "keyconfig.h"
#include "main.h"

uint8_t Fonts_GB2312_Chinese(uint8_t *text,uint8_t*fontbuf);

#ifdef TEST_GT20
void testcase_gt20(void);
#endif





#endif
